h4rm0n1c/SCSI_Experimenter/session/6e23006d-864c-4742-9457-511b329ae541/tool-results/pdf-65a604f8-ed90-4112-a40f-88b8c4090dca/page-24.jpg

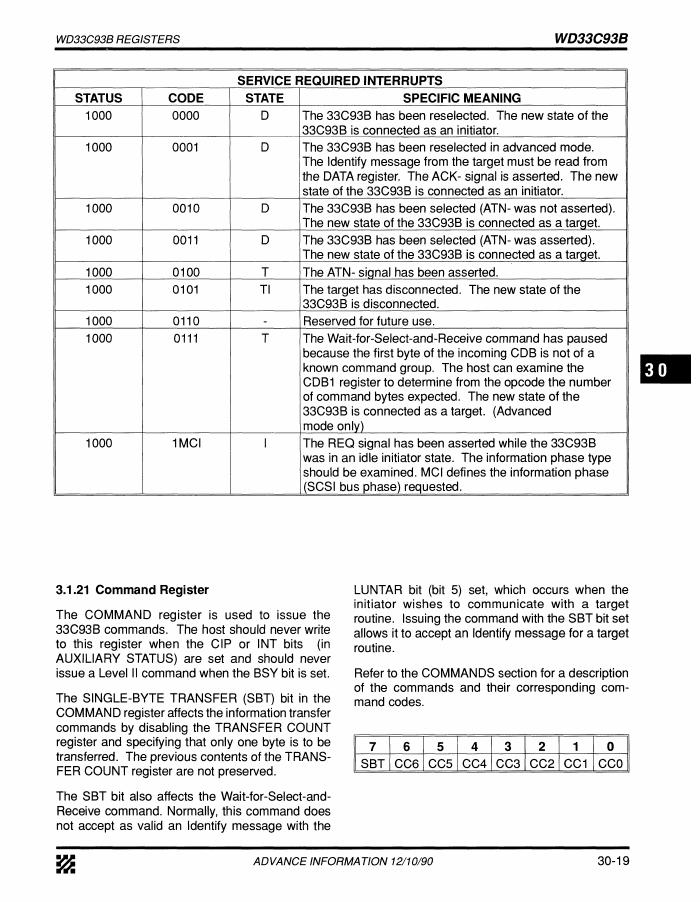
session/6e23006d-864c-4742-9457-511b329ae541/tool-results/pdf-65a604f8-ed90-4112-a40f-88b8c4090dca/page-24.jpg
