h4rm0n1c/SCSI_Experimenter/session/6e23006d-864c-4742-9457-511b329ae541/tool-results/pdf-1535076e-e012-4662-9e60-48206a4d9542/page-21.jpg

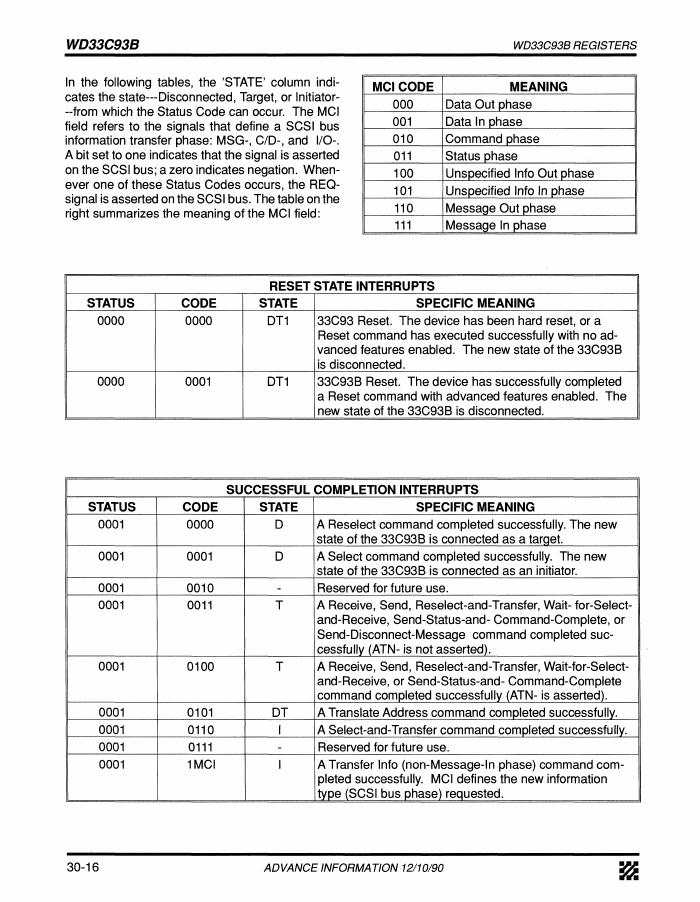
session/6e23006d-864c-4742-9457-511b329ae541/tool-results/pdf-1535076e-e012-4662-9e60-48206a4d9542/page-21.jpg
