h4rm0n1c/SCSI_Experimenter/session/6e23006d-864c-4742-9457-511b329ae541/tool-results/pdf-75530337-e969-497a-a053-e1fab07b60f2/page-57.jpg

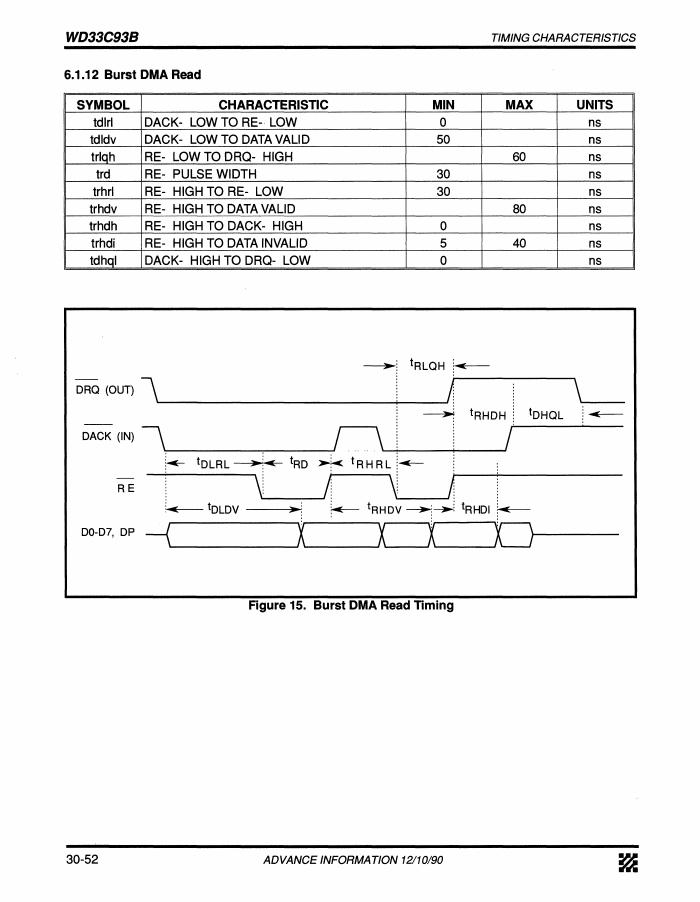
session/6e23006d-864c-4742-9457-511b329ae541/tool-results/pdf-75530337-e969-497a-a053-e1fab07b60f2/page-57.jpg
