h4rm0n1c/SCSI_Experimenter/session/6e23006d-864c-4742-9457-511b329ae541/tool-results/pdf-ae54f759-53c9-47eb-b404-9563ce885096/page-61.jpg

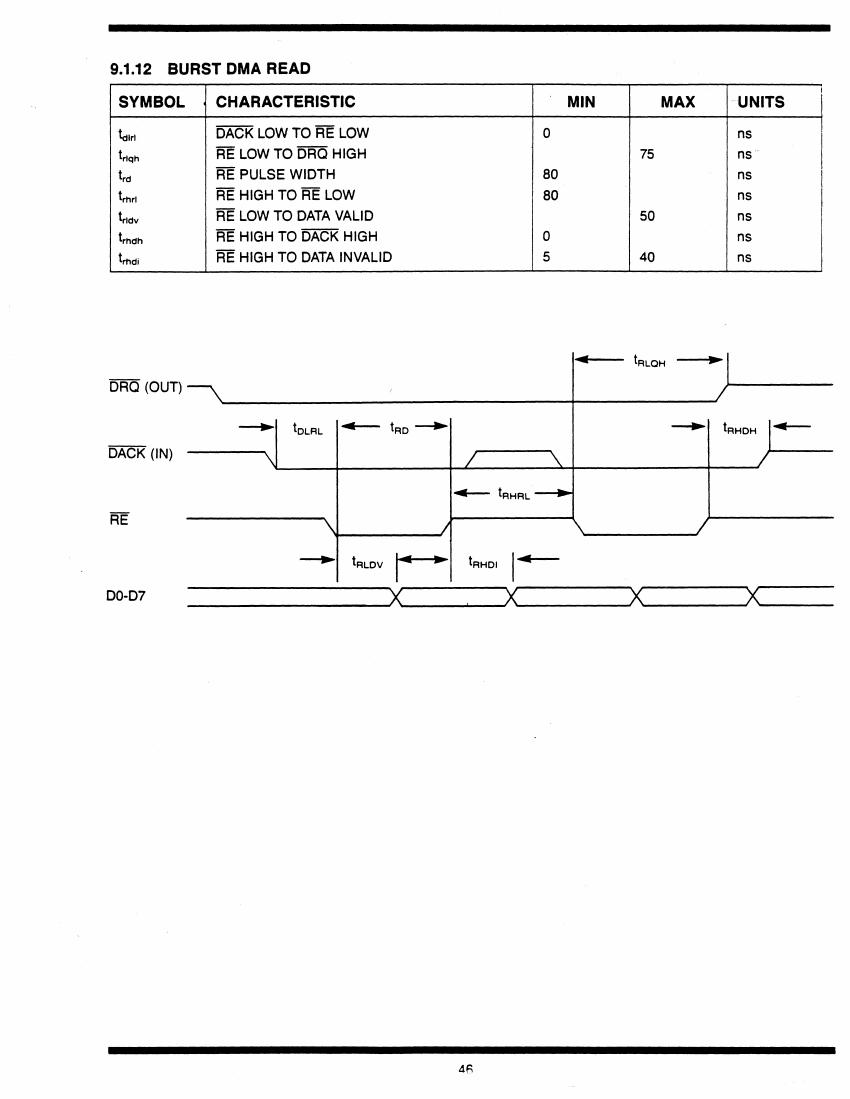
session/6e23006d-864c-4742-9457-511b329ae541/tool-results/pdf-ae54f759-53c9-47eb-b404-9563ce885096/page-61.jpg
