h4rm0n1c/SCSI_Experimenter/session/6e23006d-864c-4742-9457-511b329ae541/tool-results/pdf-c38d6c2b-facc-4b9f-be11-fba2e335aeba/page-52.jpg

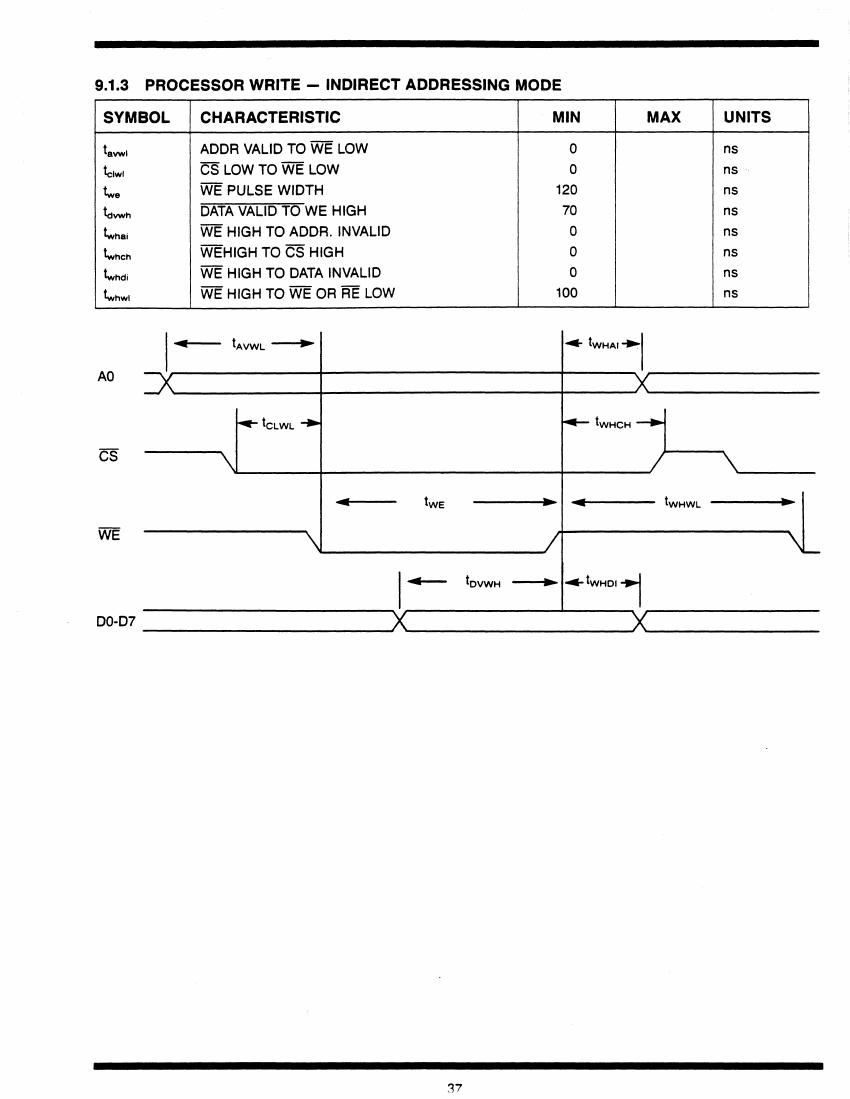
session/6e23006d-864c-4742-9457-511b329ae541/tool-results/pdf-c38d6c2b-facc-4b9f-be11-fba2e335aeba/page-52.jpg
