h4rm0n1c/SCSI_Experimenter/session/23959c13-2a44-4167-9ec7-34ddbfe380f4/tool-results/pdf-7832a5c9-73dc-41b0-9f64-26841bc13416/page-04.jpg

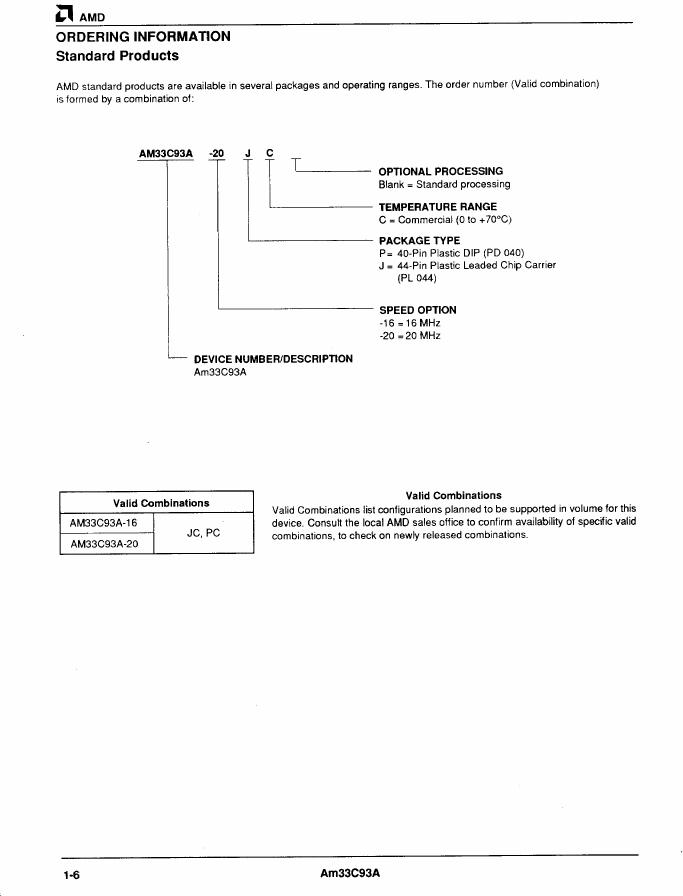
session/23959c13-2a44-4167-9ec7-34ddbfe380f4/tool-results/pdf-7832a5c9-73dc-41b0-9f64-26841bc13416/page-04.jpg
